dhuntoon/kool_keg/main/HX711.c

#include "HX711.h"
#include "esp_log.h"
#include <esp32/rom/ets_sys.h>

#define HIGH 1
#define LOW 0
#define CLOCK_DELAY_US 20

#define DEBUGTAG "HX711"

static gpio_num_t GPIO_PD_SCK = GPIO_NUM_27;	// Power Down and Serial Clock Input Pin
static gpio_num_t GPIO_DOUT = GPIO_NUM_26;		// Serial Data Output Pin
static HX711_GAIN GAIN = eGAIN_128;		// amplification factor
static unsigned long OFFSET = 8139632.00000;	// used for tare weight
//static unsigned long OFFSET = 8108536.00000;

//static unsigned long OFFSET =
//static unsigned long OFFSET = 8233286.375013;
//static unsigned long OFFSET = 0;	// used for tare weight
static float SCALE = 10000;	// used to return weight in grams, kg, ounces, whatever
//static float SCALE = 1;	// used to return weight in grams, kg, ounces, whatever

void HX711_init(gpio_num_t dout, gpio_num_t pd_sck, HX711_GAIN gain )
{
	GPIO_PD_SCK = pd_sck;
	GPIO_DOUT = dout;

	gpio_config_t io_conf;
    io_conf.intr_type =  GPIO_INTR_DISABLE;
    io_conf.mode = GPIO_MODE_OUTPUT;
    io_conf.pin_bit_mask = (1UL<<GPIO_PD_SCK);
    io_conf.pull_down_en = 0;
    io_conf.pull_up_en = 0;
    gpio_config(&io_conf);

    io_conf.intr_type =  GPIO_INTR_DISABLE;
    io_conf.pin_bit_mask = (1UL<<GPIO_DOUT);
    io_conf.mode = GPIO_MODE_INPUT;
    io_conf.pull_up_en = 0;
	gpio_config(&io_conf);

	HX711_set_gain(gain);
}

bool HX711_is_ready()
{
	return gpio_get_level(GPIO_DOUT);
}

void HX711_set_gain(HX711_GAIN gain)
{
	GAIN = gain;
	gpio_set_level(GPIO_PD_SCK, LOW);
	HX711_read();
}

uint8_t HX711_shiftIn()
{
	uint8_t value = 0;

    for(int i = 0; i < 8; ++i)
    {
        gpio_set_level(GPIO_PD_SCK, HIGH);
        ets_delay_us(CLOCK_DELAY_US);
        value |= gpio_get_level(GPIO_DOUT) << (7 - i); //get level returns
        gpio_set_level(GPIO_PD_SCK, LOW);
        ets_delay_us(CLOCK_DELAY_US);
    }

    return value;
}

unsigned long HX711_read()
{
	gpio_set_level(GPIO_PD_SCK, LOW);
	// wait for the chip to become ready
	while (HX711_is_ready())
	{
		vTaskDelay(10 / portTICK_PERIOD_MS);
	}

	unsigned long value = 0;

	//--- Enter critical section ----
	portDISABLE_INTERRUPTS();

	for(int i=0; i < 24 ; i++)
	{
		gpio_set_level(GPIO_PD_SCK, HIGH);
        ets_delay_us(CLOCK_DELAY_US);
        value = value << 1;
        gpio_set_level(GPIO_PD_SCK, LOW);
        ets_delay_us(CLOCK_DELAY_US);

        if(gpio_get_level(GPIO_DOUT))
        	value++;
	}

	// set the channel and the gain factor for the next reading using the clock pin
	for (unsigned int i = 0; i < GAIN; i++)
	{
		gpio_set_level(GPIO_PD_SCK, HIGH);
		ets_delay_us(CLOCK_DELAY_US);
		gpio_set_level(GPIO_PD_SCK, LOW);
		ets_delay_us(CLOCK_DELAY_US);
	}
	portENABLE_INTERRUPTS();
	//--- Exit critical section ----

	value =value^0x800000;

	return (value);
}



unsigned long  HX711_read_average(char times)
{
	//ESP_LOGI(DEBUGTAG, "===================== READ AVERAGE START ====================");
	unsigned long sum = 0;
	for (char i = 0; i < times; i++)
	{
			sum += HX711_read();
	}
	//ESP_LOGI(DEBUGTAG, "===================== READ AVERAGE END : %ld ====================",(sum / times));
	return sum / times;
}

unsigned long HX711_get_value(char times)
{
//	unsigned long avg = HX711_read_average(times);
//	if(avg > OFFSET)
//		return avg - OFFSET;
//	else
//		return 0;
	unsigned long avg = HX711_read_average(times);
	if(avg < OFFSET)
		return OFFSET - avg;
	else
		return 0;
}

float HX711_get_units(char times)
{
	return HX711_get_value(times) / SCALE;
}

void HX711_tare( )
{
	ESP_LOGI(DEBUGTAG, "===================== START TARE ====================");
	unsigned long sum = 0;
	sum = HX711_read_average(200);
	HX711_set_offset(sum);
	ESP_LOGI(DEBUGTAG, "===================== END TARE: %ld ====================",sum);
}

void HX711_set_scale(float scale )
{
	SCALE = scale;
}

float HX711_get_scale()
 {
	return SCALE;
}

void HX711_set_offset(unsigned long offset)
 {
	OFFSET = offset;
}

unsigned long HX711_get_offset(unsigned long offset)
{
	return OFFSET;
}

void HX711_power_down()
{
	gpio_set_level(GPIO_PD_SCK, LOW);
	ets_delay_us(CLOCK_DELAY_US);
	gpio_set_level(GPIO_PD_SCK, HIGH);
	ets_delay_us(CLOCK_DELAY_US);
}

void HX711_power_up()
{
	gpio_set_level(GPIO_PD_SCK, LOW);
}
